74kumi/Esp32-Poe-HA-Speaker/hardware/checkpoints/PoE-Speaker-Checkpoint/PoE-Speaker-RevD-eFuse-Draft/KiCad-RevD/reports/procurement-audit.md

# Procurement readiness audit

No parts have been ordered. An order code being present does not establish electrical or mechanical suitability.

- Family/base code; exact suffix or variant requires review: 4
- Missing exact order code: 127
- Order code present; ratings/footprint/availability not fully approved: 48
- PCB feature; no assembly purchase assigned: 30

Priority: finalize U1 module variant, U5 amplifier package/order suffix, U9/U10 order suffixes, F1 fuse and protection passives. Check C1-C6 package metadata against their actual radial footprints; older source descriptions may still say SMD.

| Reference | Value | Issue |
|---|---|---|
| C10 | 220nF | Missing exact order code |
| C100 | 22nF | Missing exact order code |
| C101 | 6.8nF | Missing exact order code |
| C102 | 10nF | Missing exact order code |
| C103 | 4.7uF | Missing exact order code |
| C104 | 10nF | Missing exact order code |
| C105 | 100nF | Missing exact order code |
| C106 | 100nF | Missing exact order code |
| C107 | 100nF | Missing exact order code |
| C108 | 100nF | Missing exact order code |
| C109 | 100nF | Missing exact order code |
| C11 | 1uF | Missing exact order code |
| C110 | 100nF | Missing exact order code |
| C111 | 10uF | Missing exact order code |
| C112 | 100nF | Missing exact order code |
| C113 | 10uF | Missing exact order code |
| C114 | 1uF | Missing exact order code |
| C115 | 100nF | Missing exact order code |
| C12 | 1uF | Missing exact order code |
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
| R32 | 33Ω | Missing exact order code |
| R33 | 4.7kΩ | Missing exact order code |
| R34 | 4.7kΩ | Missing exact order code |
| R35 | 100kΩ | Missing exact order code |
| R36 | 100kΩ | Missing exact order code |
| R38 | 10kΩ | Missing exact order code |
| R4 | 27kΩ | Missing exact order code |
| R5 | 27kΩ | Missing exact order code |
| R6 | 10kΩ | Missing exact order code |
| R7 | 10kΩ | Missing exact order code |
| R8 | 10kΩ | Missing exact order code |
| R9 | 10kΩ | Missing exact order code |
| U1 | Ag5800 | Family/base code; exact suffix or variant requires review |
| U10 | LM5050-2 | Family/base code; exact suffix or variant requires review |
| U5 | TPA3116D2 | Family/base code; exact suffix or variant requires review |
| U9 | LM5050-2 | Family/base code; exact suffix or variant requires review |
