74kumi/Esp32-Poe-HA-Speaker/docs/images/early-board-render.png

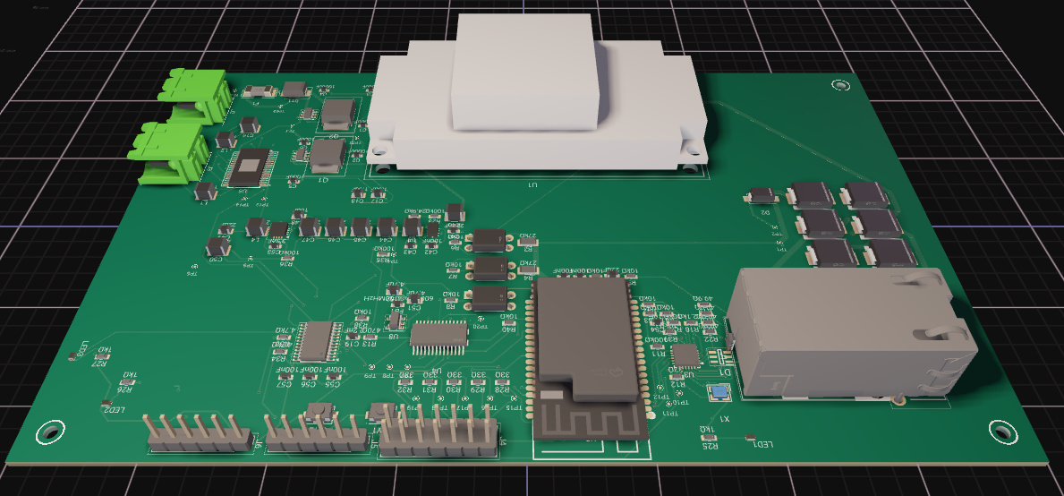
docs/images/early-board-render.png
