74kumi/Esp32-Poe-HA-Speaker/hardware/checkpoints/PoE-Speaker-Checkpoint/PoE-Speaker-RevC-Integrated-Draft/KiCad-RevC/reports/bench-protection-detail.png

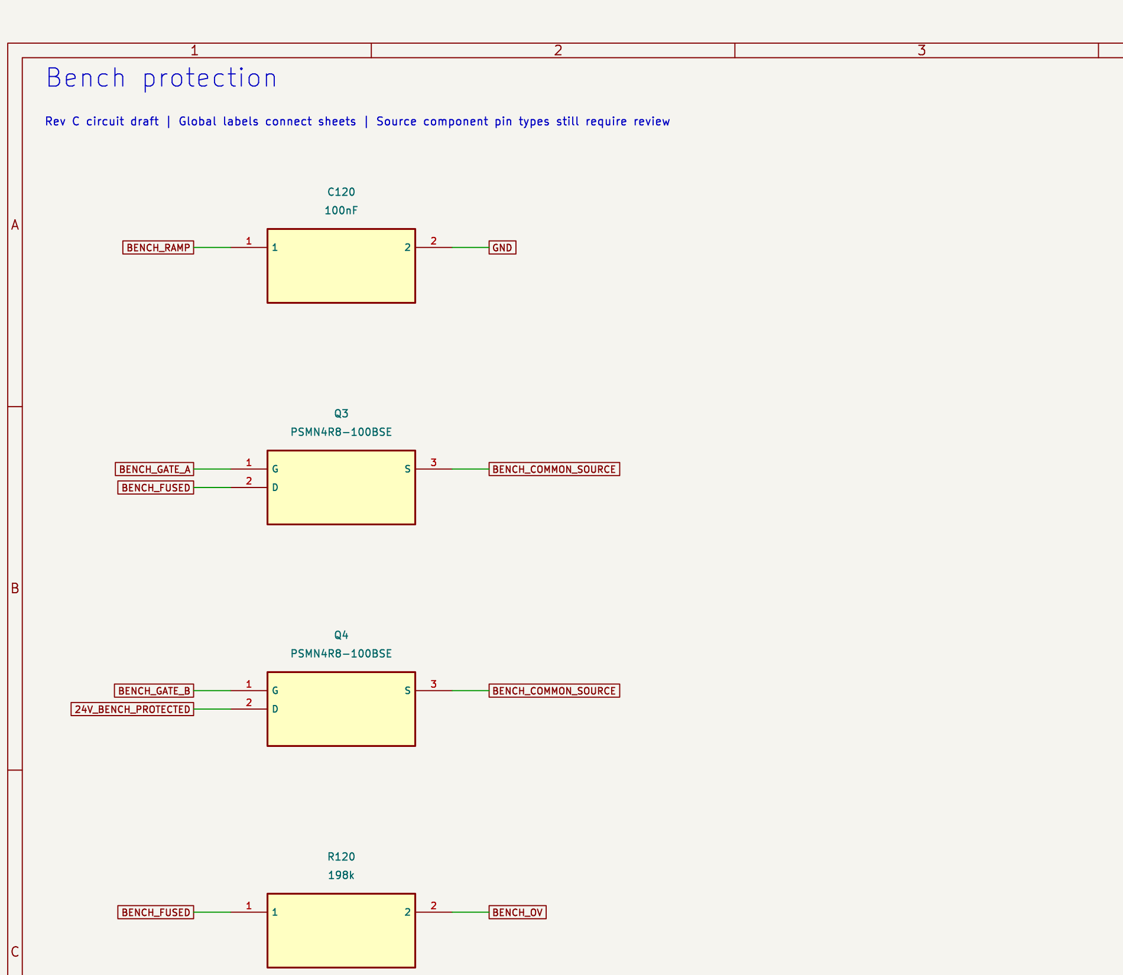
hardware/checkpoints/PoE-Speaker-Checkpoint/PoE-Speaker-RevC-Integrated-Draft/KiCad-RevC/reports/bench-protection-detail.png
