74kumi/Esp32-Poe-HA-Speaker/hardware/checkpoints/PoE-Speaker-Checkpoint/PoE-Speaker-RevD-eFuse-Draft/KiCad-RevD/reports/efuse-schematic.png

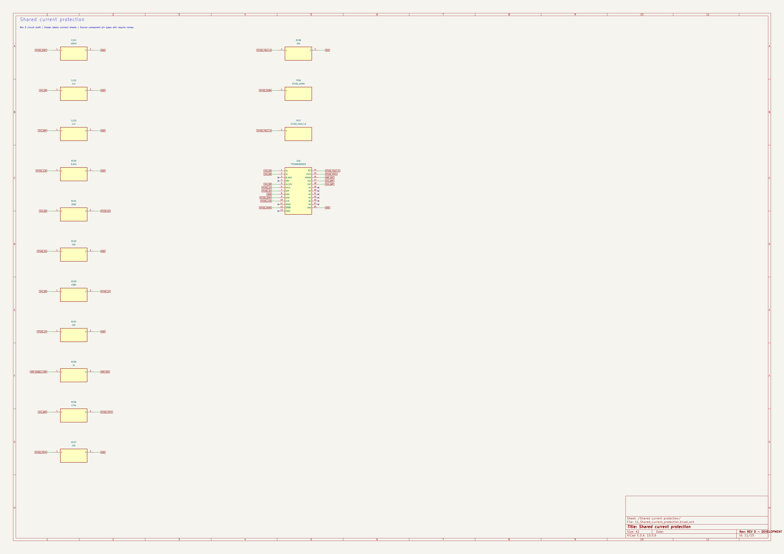
hardware/checkpoints/PoE-Speaker-Checkpoint/PoE-Speaker-RevD-eFuse-Draft/KiCad-RevD/reports/efuse-schematic.png
