74kumi/Esp32-Poe-HA-Speaker/hardware/checkpoints/PoE-Speaker-Checkpoint/PoE-Speaker-RevE-Review/engineering/accept_c14_c15_ground.py

from pathlib import Path
import json,pcbnew as p,shutil
D=Path('KiCad-RevE');E=Path('engineering');b=p.LoadBoard(str(D/'power-trial.kicad_pcb'));z=next(z for z in b.Zones() if z.GetNetname()=='GND' and z.GetLayer()==p.In1_Cu);rows=[]
for ref,y in [('C14',115.5),('C15',111.5)]:
 pos=p.VECTOR2I(p.FromMM(197.425),p.FromMM(y));v=next(t for t in b.GetTracks() if isinstance(t,p.PCB_VIA) and t.GetPosition()==pos);inside=z.HitTestFilledArea(p.In1_Cu,pos);assert inside,(ref,'not in filled ground');rows.append({'reference':ref,'via_uuid':v.m_Uuid.AsString(),'position_mm':[197.425,y],'diameter_mm':.8,'drill_mm':.4,'track_width_mm':.6,'track_length_mm':1.1,'center_in_filled_ground_plane':inside})
d=json.loads((D/'reports/power-trial-drc.json').read_text());assert not d['violations'] and not d['unconnected_items'];(D/'reports/c14-c15-ground-vias.json').write_text(json.dumps({'changes':rows,'limitation':'Filled-zone contact and DRC checked; no return-current distribution or inductance qualification.'},indent=2));backup=D/'before-c14-c15-ground-vias.kicad_pcb';assert not backup.exists();shutil.copy2(D/'PoE-Speaker-RevE.kicad_pcb',backup);shutil.copy2(D/'power-trial.kicad_pcb',D/'PoE-Speaker-RevE.kicad_pcb')
with (E/'REVE-TRUNK-ROUTING.md').open('a',encoding='utf-8') as f:f.write('\n\n## Accepted C14/C15 local ground vias — 2026-09-14\n\nAdded 0.8 mm copper / 0.4 mm drill GND vias at (197.425,115.5) and (197.425,111.5), each with a 1.1 mm long, 0.6 mm wide F.Cu link from its capacitor ground pad. Hole-to-pad guard checked. Initial x=197.325 conflicted with the bottom 3V3 trunk and was rejected; x=197.425 passes. Both via centers hit the saved filled In1.Cu GND zone. Final DRC zero, unconnected zero. Existing ground routes retained. See reports/c14-c15-ground-vias.json. Backup before-c14-c15-ground-vias.kicad_pcb. Ground return distribution and amplifier pin/plane access remain for review.\n')
f=E/'package_prototype_review.py';s=f.read_text().replace('Next: prioritize C14/C15 local ground access and verify amplifier ground-plane continuity using reports/amplifier-ground-access.json;', 'Next: verify amplifier ground-pin access and ground-plane continuity. C14/C15 now have accepted local 0.8/0.4 mm ground vias with 1.1 mm, 0.6 mm wide links; both contact the filled In1 GND zone (reports/c14-c15-ground-vias.json). Use reports/amplifier-ground-access.json;');f.write_text(s)
