74kumi/Esp32-Poe-HA-Speaker/hardware/checkpoints/PoE-Speaker-Checkpoint/PoE-Speaker-RevE-Review/engineering/accept_efuse_via.py

from pathlib import Path
import json,shutil
D=Path('KiCad-RevE');E=Path('engineering');d=json.loads((D/'reports/power-trial-drc.json').read_text());assert not d['violations'] and not d['unconnected_items'];backup=D/'before-efuse-via-relocation.kicad_pcb';assert not backup.exists();shutil.copy2(D/'PoE-Speaker-RevE.kicad_pcb',backup);shutil.copy2(D/'power-trial.kicad_pcb',D/'PoE-Speaker-RevE.kicad_pcb')
f=D/'reports/power-via-review.json';r=json.loads(f.read_text());v=next(x for x in r['vias'] if x['uuid']=='b983fee9-a187-486f-966c-0b0f0547dc19');v.update(final_position_mm=[256.4755,78.1546],final_diameter_mm=.8,final_drill_mm=.4,changed=True,reason='Moved 0.08 mm upward; preserved long In2 route and added 0.6 mm connecting segment. Pad-hole margin checked at 0.30 mm from center.');r['validation']['changed_vias']=12;f.write_text(json.dumps(r,indent=2))
with (E/'REVE-TRUNK-ROUTING.md').open('a',encoding='utf-8') as f:f.write('\n\n## Accepted eFuse output via relocation — 2026-09-14\n\nVia b983fee9 moved from (256.4755,78.2346) to (256.4755,78.1546), enlarged from 0.6/0.3 mm copper/drill to 0.8/0.4 mm. Preserved the original long In2 route to clear EFUSE_FAULT_N; added a 0.08 mm long, 0.6 mm wide connecting segment. F.Cu endpoint follows the shifted via. Checked new hole against all pad bounding boxes with 0.30 mm center margin. Larger displacements approached C123 and were rejected. Final DRC zero and unconnected zero. This brings the preceding power-via review to twelve improvements and six original constrained vias. Backup: before-efuse-via-relocation.kicad_pcb. No via ampacity claim; plating and thermal assumptions remain unresolved.\n')
f=E/'package_prototype_review.py';s=f.read_text().replace('seven remaining constrained load-path vias','six remaining constrained load-path vias').replace('Eleven load-path vias have accepted larger drills/copper pads','Twelve load-path vias have accepted larger drills/copper pads, including the relocated eFuse output via');f.write_text(s)
