74kumi/Esp32-Poe-HA-Speaker/hardware/checkpoints/PoE-Speaker-Checkpoint/PoE-Speaker-RevE-Review/engineering/update_release_review.py

from pathlib import Path
E=Path('engineering');f=E/'package_prototype_review.py';s=f.read_text();s=s.replace('F1 still has its imported code and needs a substantiated DC breaking/rating review.', 'F1 DC interrupt ratings are now sourced; source/fault and time-current coordination remain open (engineering/FUSE-RATING-REVIEW.md).');s=s.replace('The 210x100mm board extension has no additional mounting holes yet.', 'H3/H4 now support the extended right edge at x=275; use insulating M2 standoffs. Thirteen assembly components still need verified courtyard/body review.');s=s.replace('Next: review remaining amplifier ground-pin-to-plane paths', 'Next: prioritize Ethernet differential routing/stackup and the concrete release blockers in engineering/ORDER-RELEASE-REVIEW.md. Mounting and eight rectifier courtyards are updated. After that, review remaining amplifier ground-pin-to-plane paths');s=s.replace("not f.name.startswith(('before-','power-trial'))", "not any(part.startswith(('before-','power-trial')) for part in f.parts)");f.write_text(s)
f=E/'checkpoint_reve.py';s=f.read_text().replace("'audit_amp_ground_plane.py',", "'audit_amp_ground_plane.py','audit_ethernet_routing.py','audit_ethernet_paths.py','audit_courtyard_coverage.py',");f.write_text(s)
f=E/'audit_courtyard_coverage.py';s=f.read_text().replace('print(json.dumps(rows,indent=2))',"print('Missing courtyards:',len(rows),'including',sum(not x['board_feature'] for x in rows),'assembly components')");f.write_text(s)
f=E/'FABRICATION-PROCESS.md';s=f.read_text().replace('five schematic ERC findings', 'remaining imported-symbol electrical review (saved ERC now zero)');s+='\nCurrent release priorities and evidence: ORDER-RELEASE-REVIEW.md. F1 manufacturer DC ratings are sourced in FUSE-RATING-REVIEW.md; coordination remains open.\n';f.write_text(s)
f=E/'SECONDARY-RAIL-REVIEW.md';s=f.read_text();s='> Historical review. Superseded items: U7 FSW is now tied to 3V3; saved ERC is zero following source review/annotations. Remaining regulator-loop/stability checks below are still open. See ORDER-RELEASE-REVIEW.md for current release status.\n\n'+s;f.write_text(s)
